UAlberta-EcoCar/Auxillary-Power-Board/Atmel Studio/LCD_I2C_Arduino/ssd1306_128x32_i2c/ADCRead.h

#ifndef ADCREAD_H_
#define ADCREAD_H_

	#ifdef __cplusplus
	extern "C"{
	#endif

		#include <avr/io.h>

		//Function reads and samples the ADC, returning a 10bit value (stored as uint16)
		//The input is the pin number of the ADC to be read.
		uint16_t extern ADCRead(uint8_t pin);


	#ifdef __cplusplus
	}
	#endif


#endif 
